sebastianha/power-bank-sensor-node/images/0040.jpg

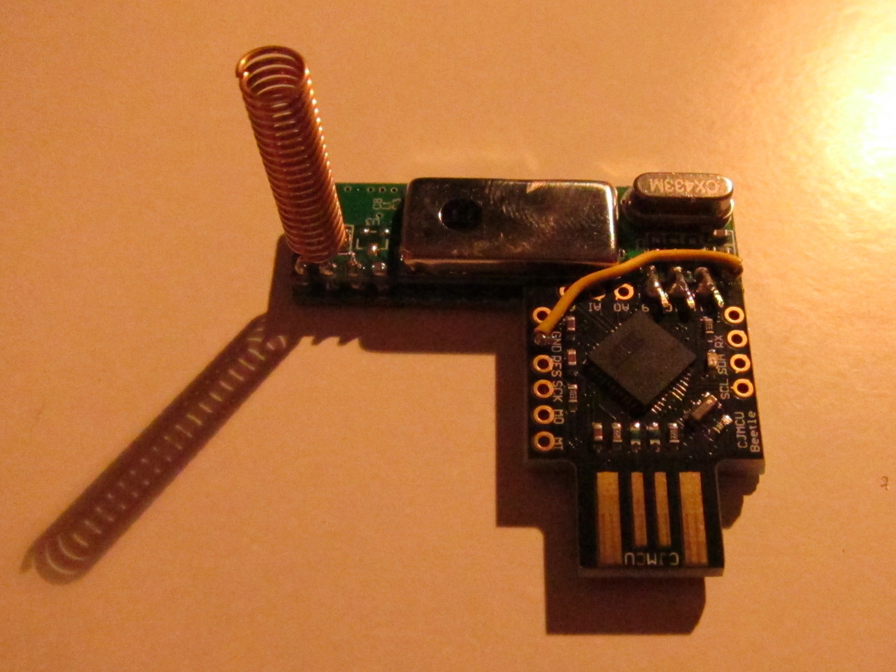
images/0040.jpg
